jnwatts/horu/photos/IMG_20170226_180400.jpg

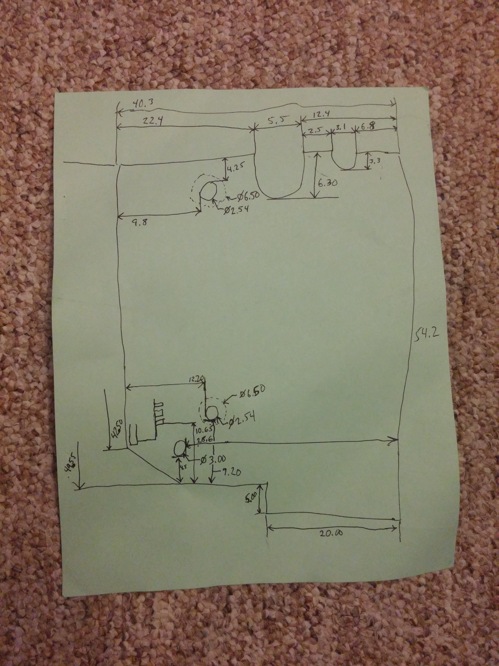
photos/IMG_20170226_180400.jpg
